giorgio323323/ARI_V3/00_doc/_spuntiDiLavoro/loges_PavimentiTattili/LogesIdea.docx

Giorgio Rancilio

Giorgio323@gmail.com

Lo spunto:

Usare i pavimenti tattili come guida per Arianna

Il sistema di pavimenti tattili si chiama SISTEMA LOGES: Linea di Orientamento Guida e Sicurezza

Link

https://en.wikipedia.org/wiki/Tactile_paving
