giorgio323323/ARI_V3/00_doc/dataSheet/dimensioniServo.jpg

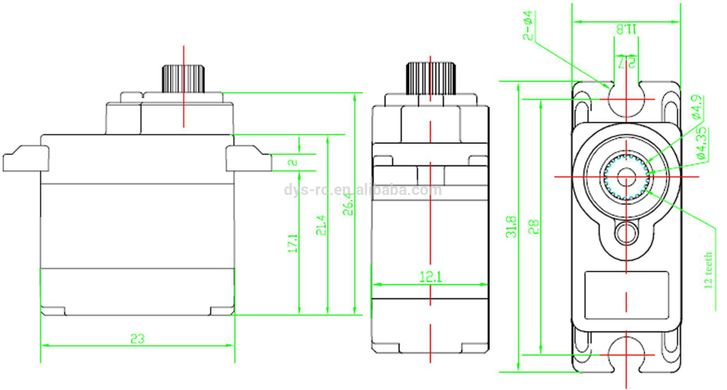
00_doc/dataSheet/dimensioniServo.jpg
