giorgio323323/ARI_V3/00_doc/docUsoCostruzione/Photos/IMG_20181124_100131.jpg

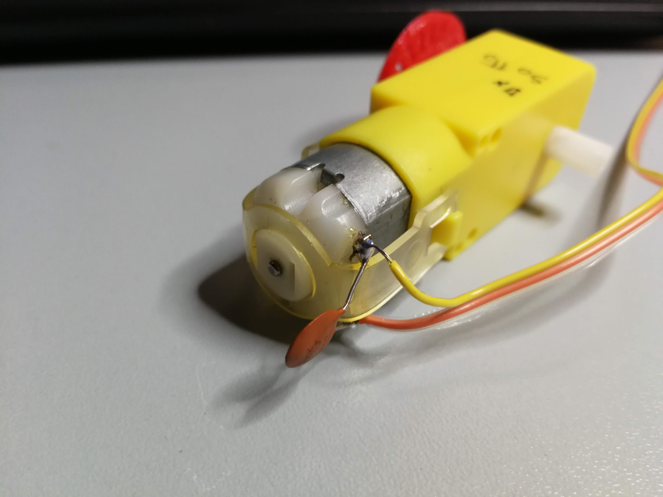
00_doc/docUsoCostruzione/Photos/IMG_20181124_100131.jpg
