giorgio323323/ARI_V3/01_pcSoftware/arianna_cli_socket2.2/scheda/images/freccia-che-punta-verso-sinistra.jpg

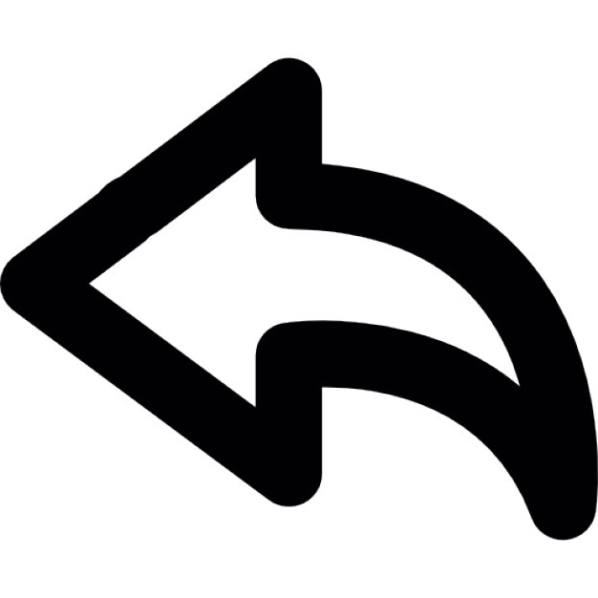
01_pcSoftware/arianna_cli_socket2.2/scheda/images/freccia-che-punta-verso-sinistra.jpg
