giorgio323323/ARI_V3/01_pcSoftware/arianna_cli_socket2.2/scheda/images/freccia-in-alto.jpg

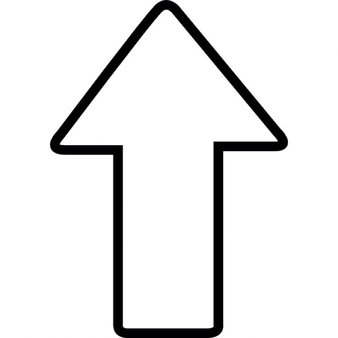
01_pcSoftware/arianna_cli_socket2.2/scheda/images/freccia-in-alto.jpg
