giorgio323323/ARI_V3/01_pcSoftware/arianna_cli_socket2.2/scheda/images/img0001.png

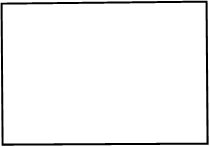
01_pcSoftware/arianna_cli_socket2.2/scheda/images/img0001.png
