giorgio323323/ARI_V3/01_pcSoftware/arianna_cli_socket2.2/scheda/images/reset.jpg

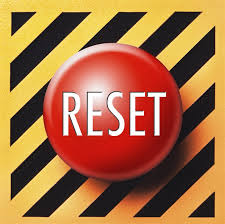
01_pcSoftware/arianna_cli_socket2.2/scheda/images/reset.jpg
