giorgio323323/ARI_V3/05_pcb/shieldAtmegaArianna_02p1_board.png

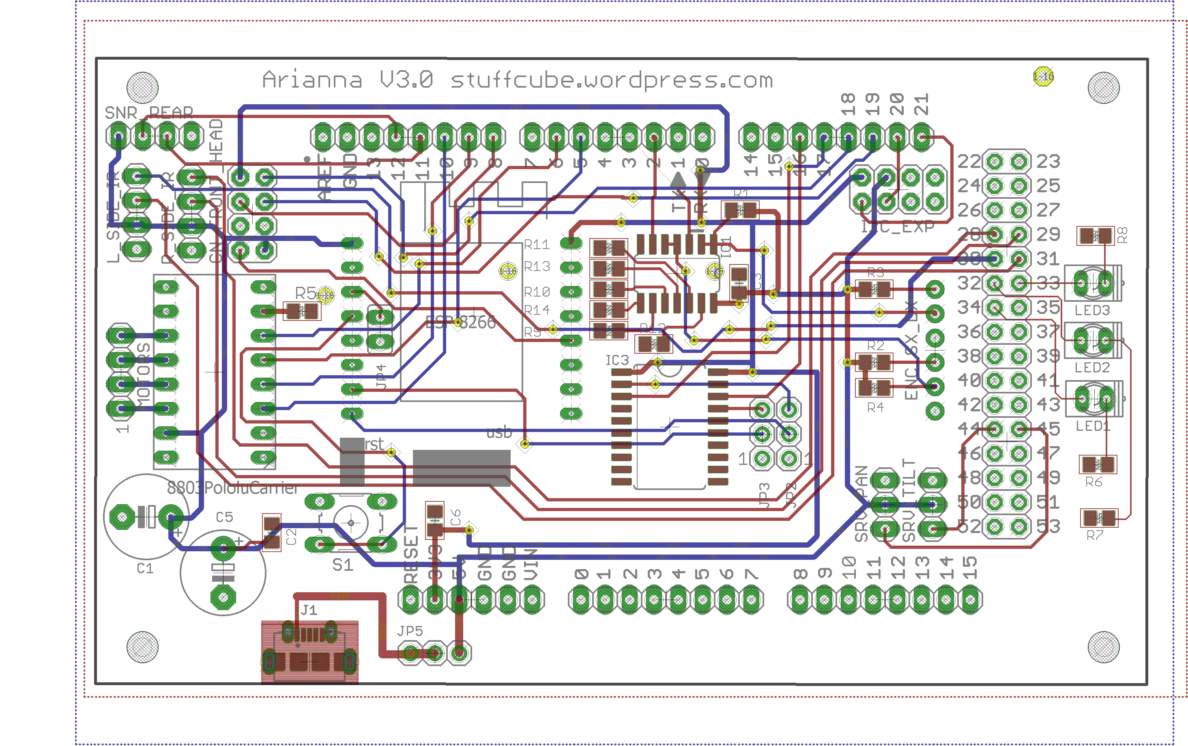
05_pcb/shieldAtmegaArianna_02p1_board.png
